suzan-works/USB-C_PCB_Receptacle/kicad/USB-C_PCB_Receptacle.kicad_sch

## KiCad design kicad/USB-C_PCB_Receptacle.kicad_sch (2025-02-07)

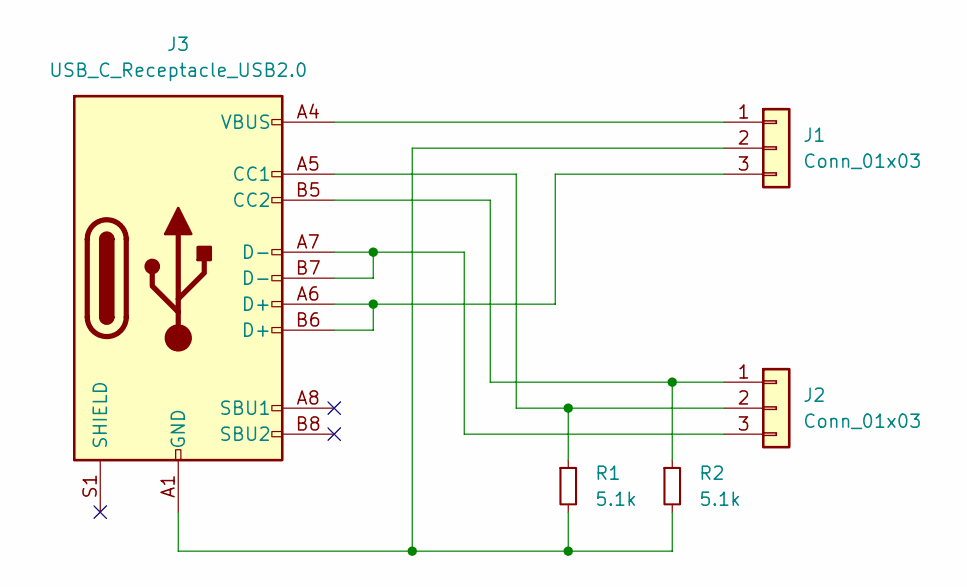
[picture p7: schematic USB-C_PCB_Receptacle.kicad_sch]

Parts:
J1, J2: Conn_01x03; PinHeader_1x03_P2.54mm_Vertical
J3: USB_C_Receptacle_USB2.0; USB-C_PCBPLUG
R1, R2: 5.1k; R_0603_1608Metric

Connections:
unnamed: J1.1, J3.A4 (VBUS), J3.A9 (VBUS), J3.B4 (VBUS), J3.B9 (VBUS)
unnamed: J1.2, J3.A1 (GND), J3.A12 (GND), J3.B1 (GND), J3.B12 (GND), R1.2, R2.2
unnamed: J1.3, J3.A6 (D+), J3.B6 (D+)
unnamed: J2.1, J3.B5 (CC2), R2.1
unnamed: J2.2, J3.A5 (CC1), R1.1
unnamed: J2.3, J3.A7 (D-), J3.B7 (D-)
